dshop-gliwice/smogbusters/docs/images/smogbuster-prototype-800px.png

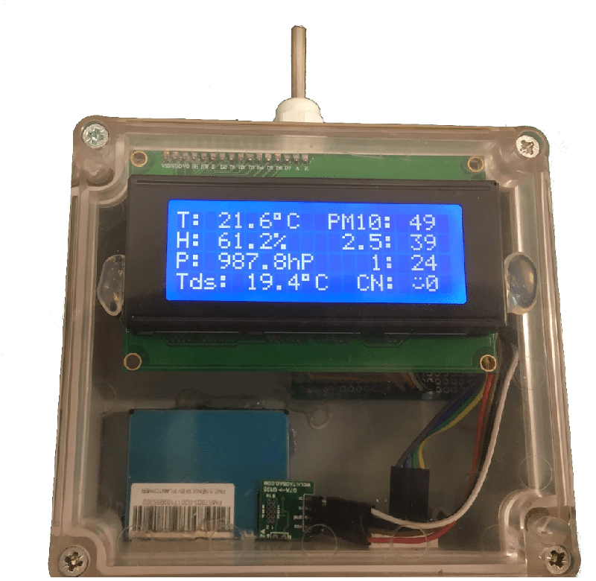
docs/images/smogbuster-prototype-800px.png
